sportiduino/sportiduino/img/BaseStationBatHolderFixed.jpg

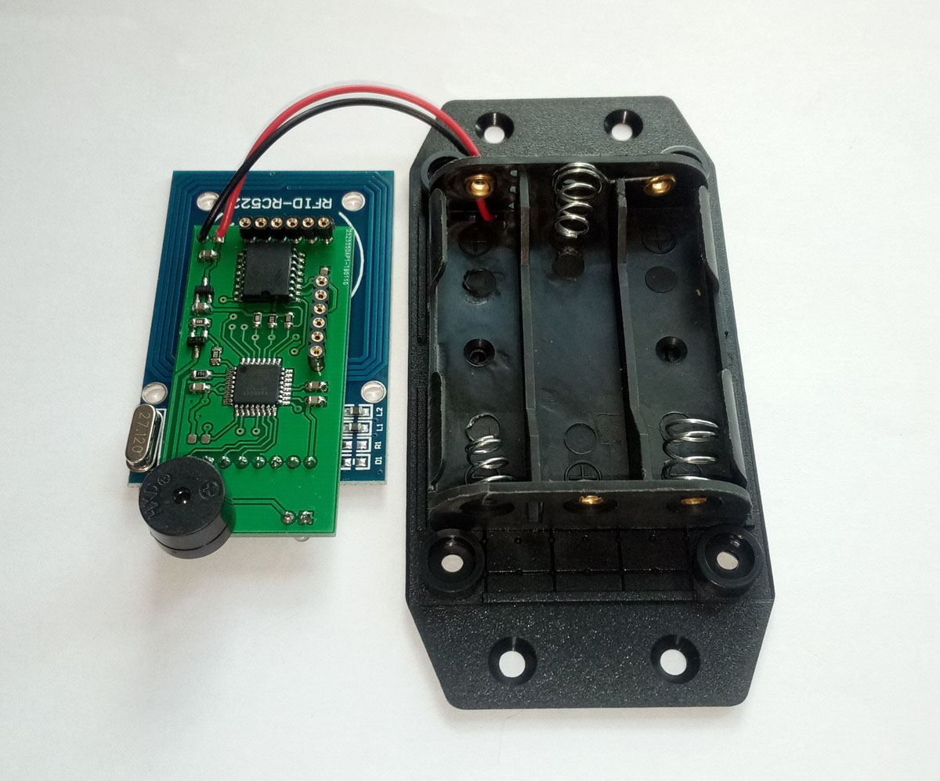
img/BaseStationBatHolderFixed.jpg
