sportiduino/sportiduino/img/BaseStationSerialConfConnect.jpg

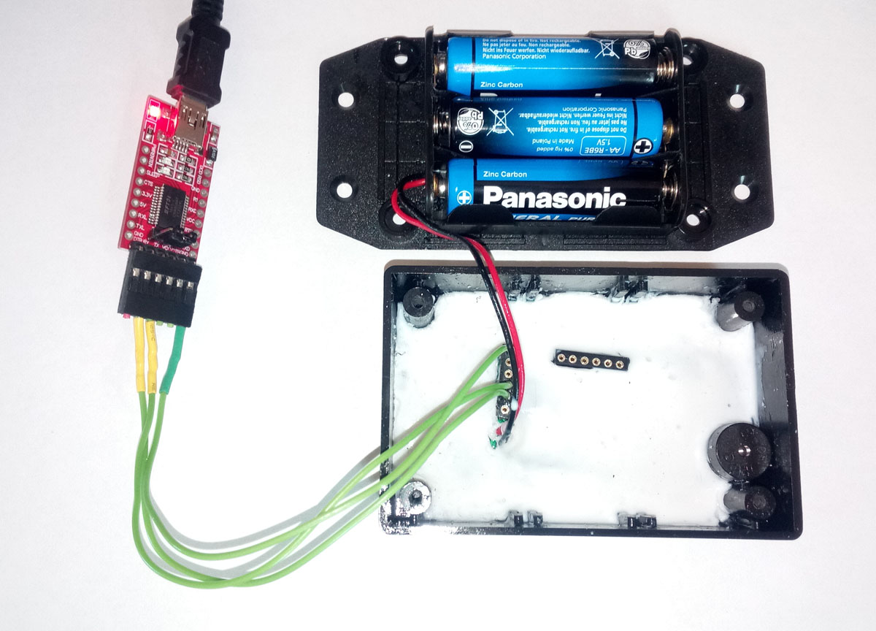
img/BaseStationSerialConfConnect.jpg
