sportiduino/sportiduino/img/BaseStationSoldedBottom.jpg

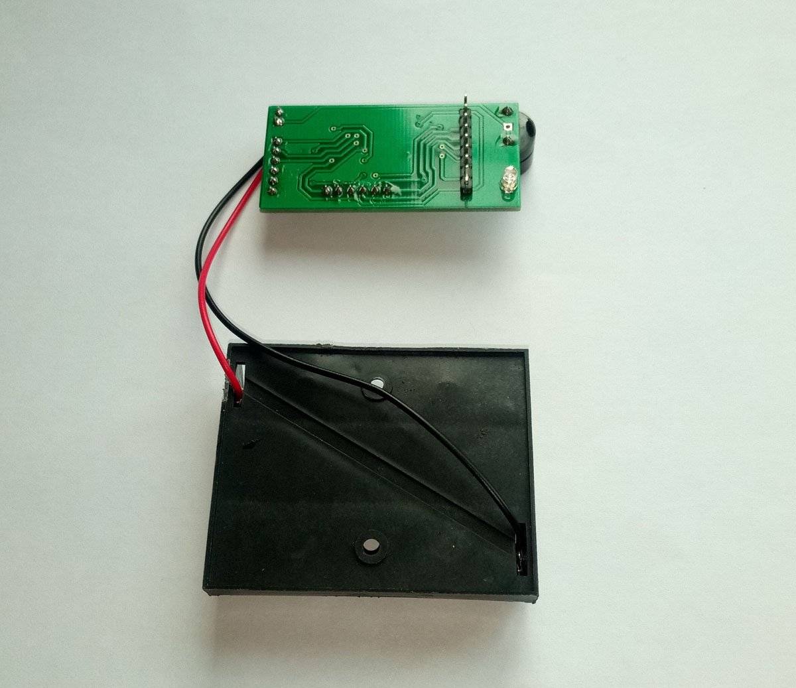
img/BaseStationSoldedBottom.jpg
