sportiduino/sportiduino/img/BaseStationSoldedTop.jpg

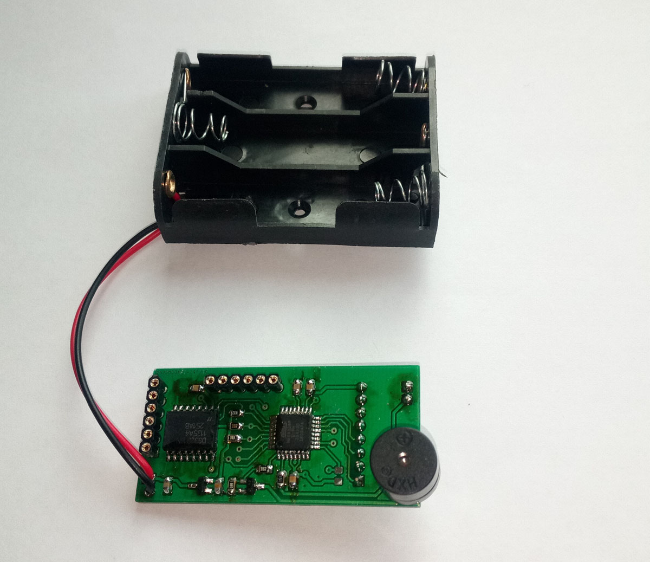
img/BaseStationSoldedTop.jpg
