sportiduino/sportiduino/img/Breadboard.JPG

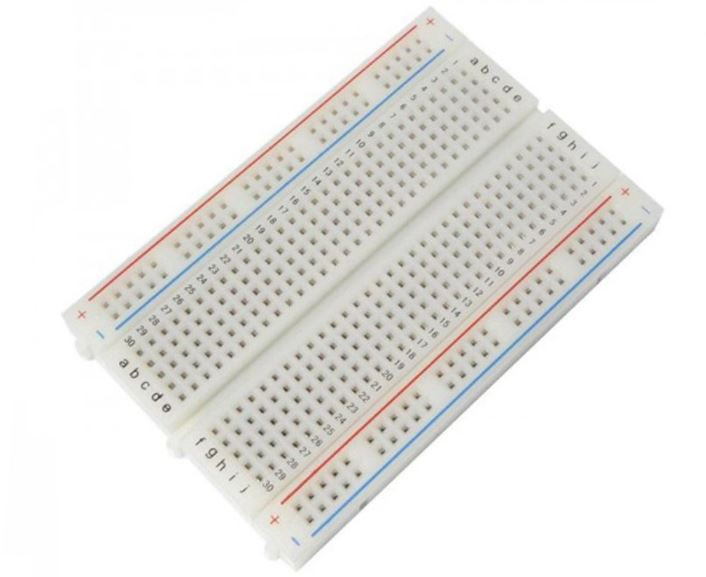
img/Breadboard.JPG
