sportiduino/sportiduino/img/ConfigWire.jpg

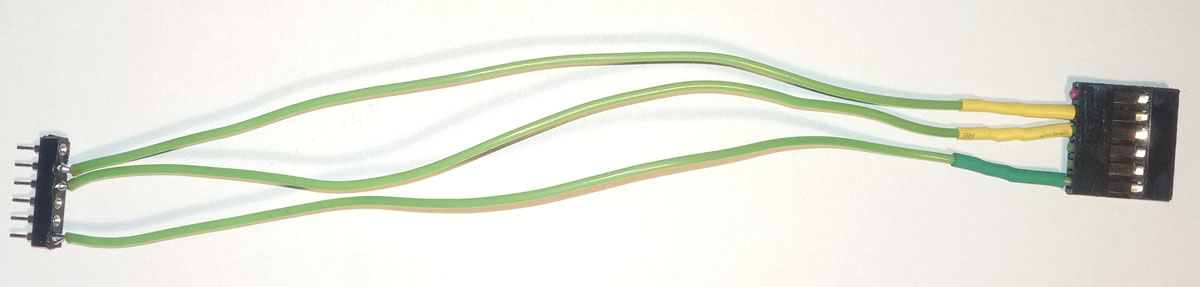
img/ConfigWire.jpg
