sportiduino/sportiduino/img/IntEEPROM.JPG

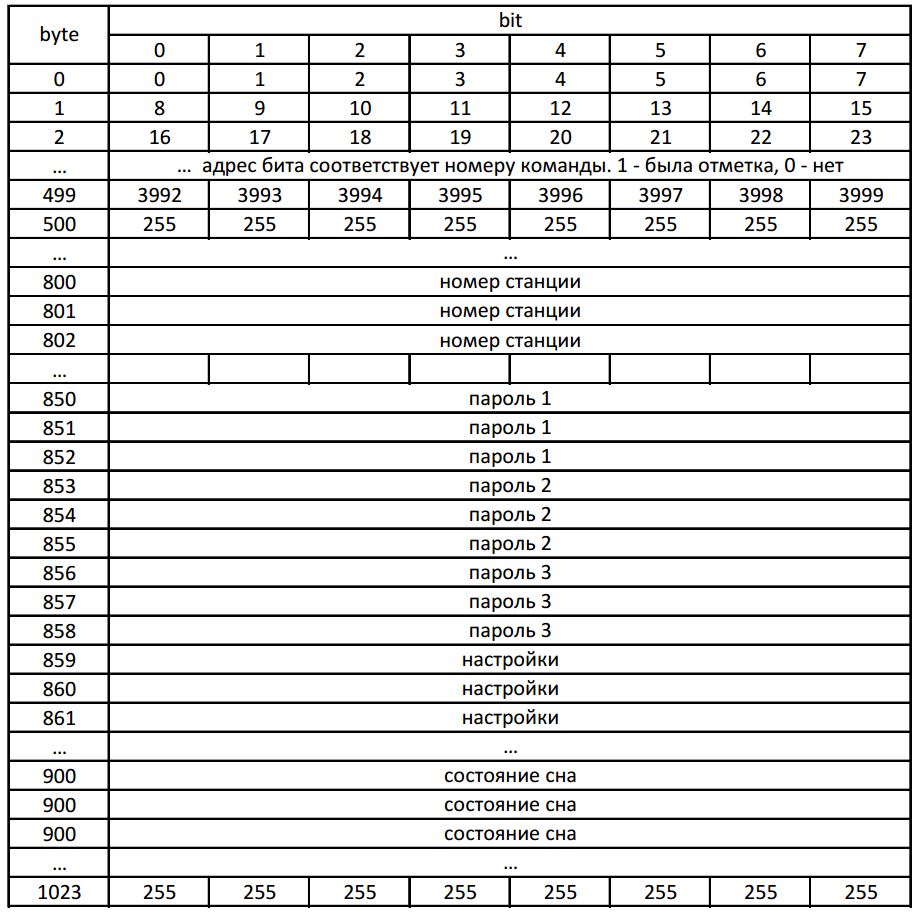
img/IntEEPROM.JPG
