sportiduino/sportiduino/img/ntag-dumpchip.jpg

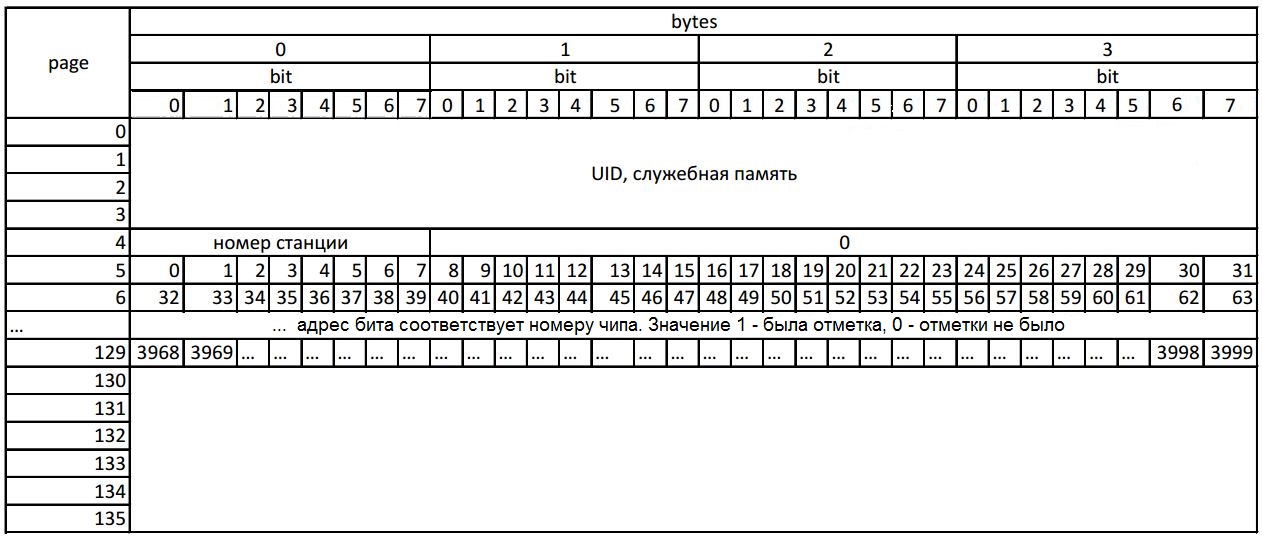
img/ntag-dumpchip.jpg
