sportiduino/sportiduino/img/pq_ru_master.png

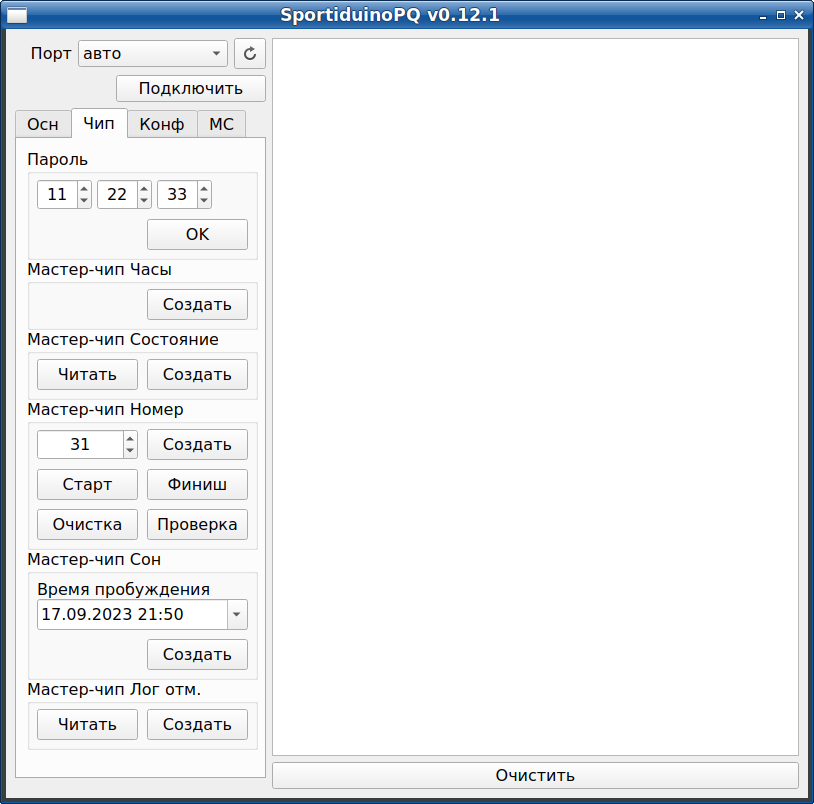
img/pq_ru_master.png
