sportiduino/sportiduino/img/s03.jpg

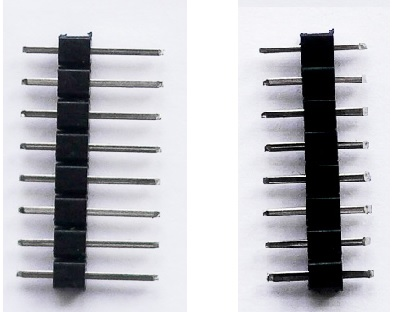
img/s03.jpg
