sportiduino/sportiduino/img/s04.jpg

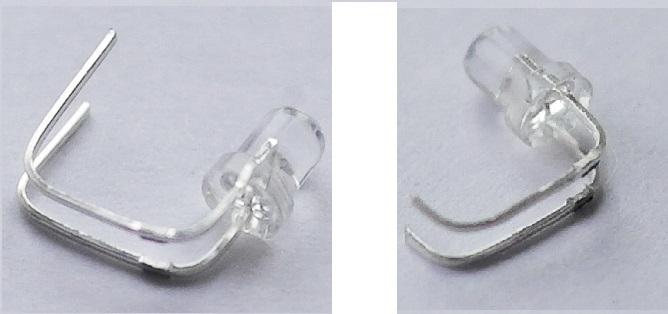
img/s04.jpg
