sportiduino/sportiduino/img/s05.jpg

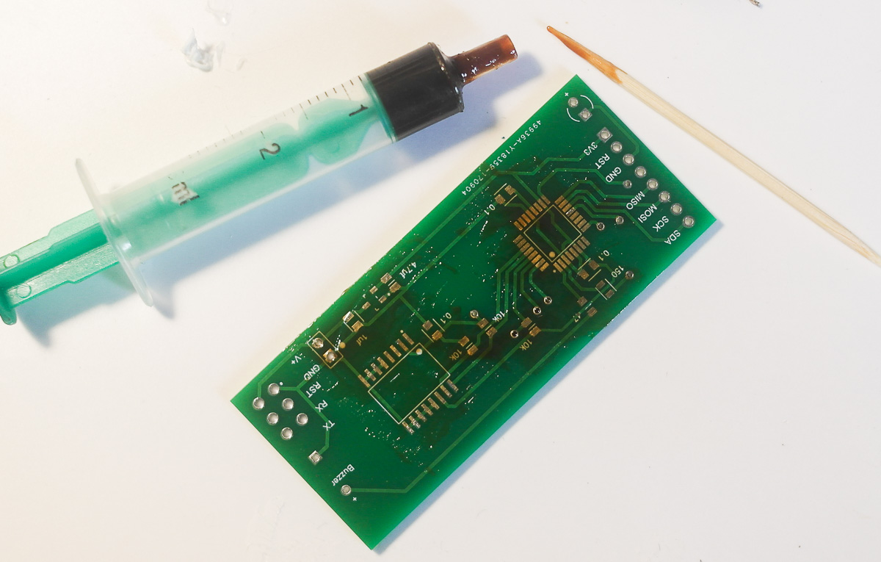
img/s05.jpg
