sportiduino/sportiduino/img/s06.jpg

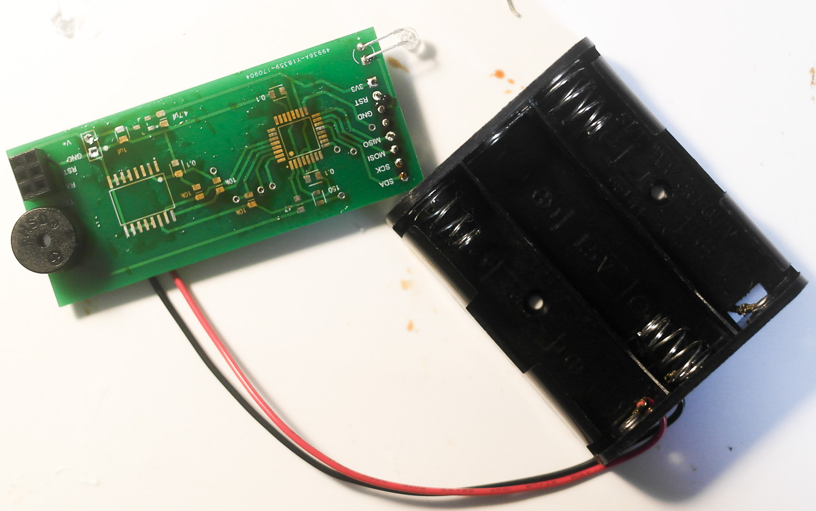
img/s06.jpg
