sportiduino/sportiduino/img/s07.jpg

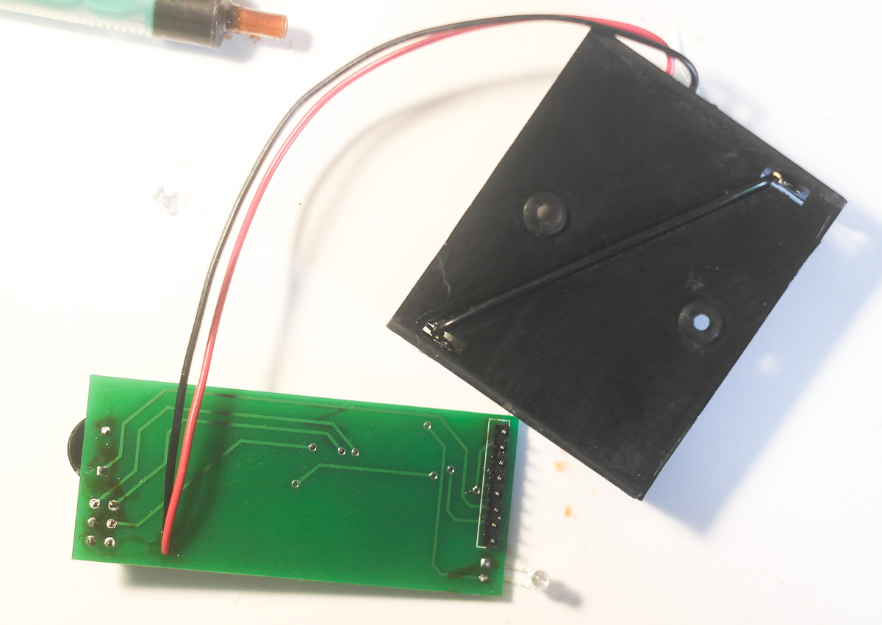
img/s07.jpg
