sportiduino/sportiduino/img/s09.jpg

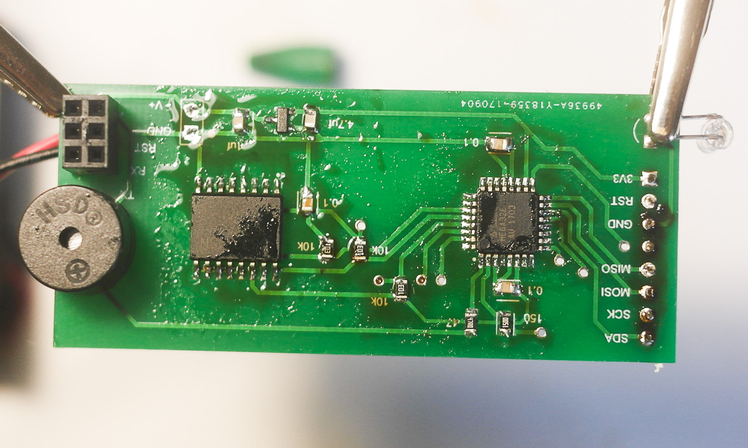
img/s09.jpg
