sportiduino/sportiduino/img/s10.jpg

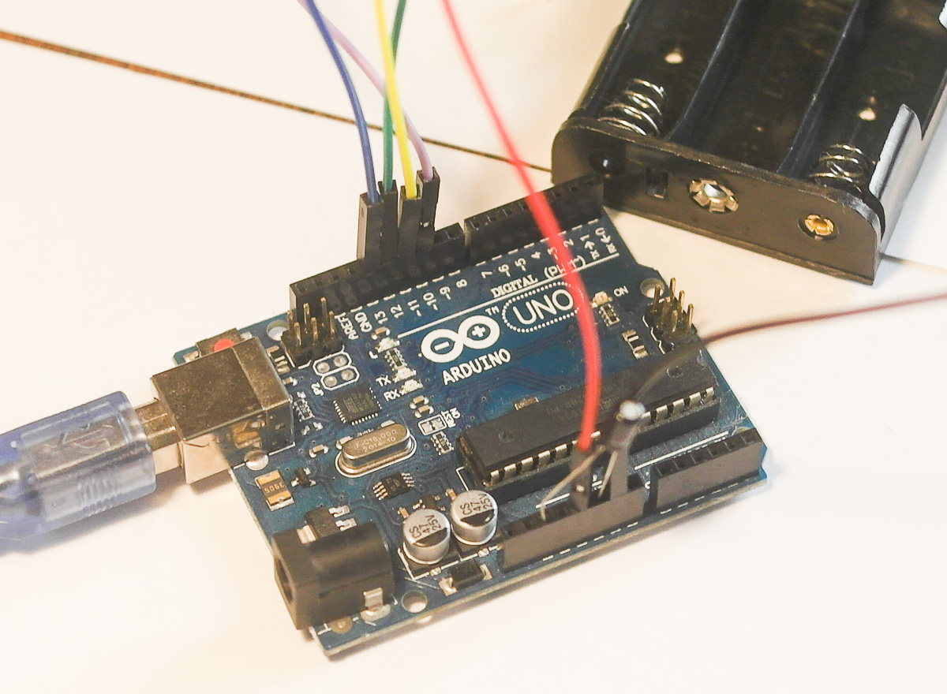
img/s10.jpg
