sportiduino/sportiduino/img/s11.jpg

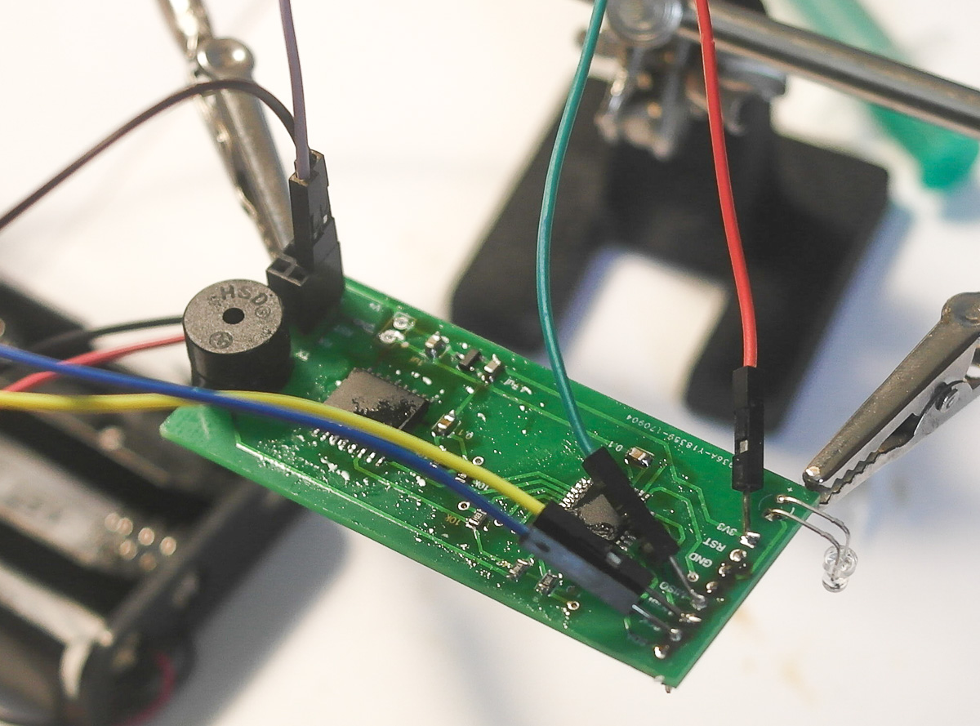
img/s11.jpg
