sportiduino/sportiduino/img/s12.jpg

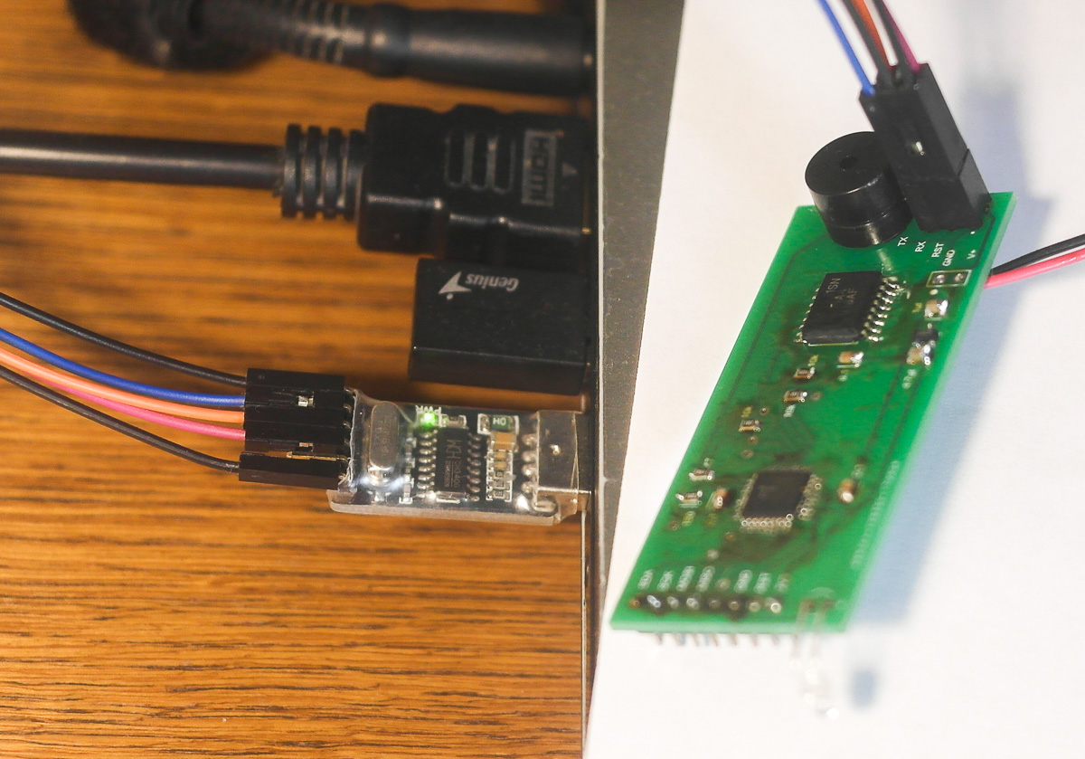
img/s12.jpg
