sportiduino/sportiduino/img/s13.jpg

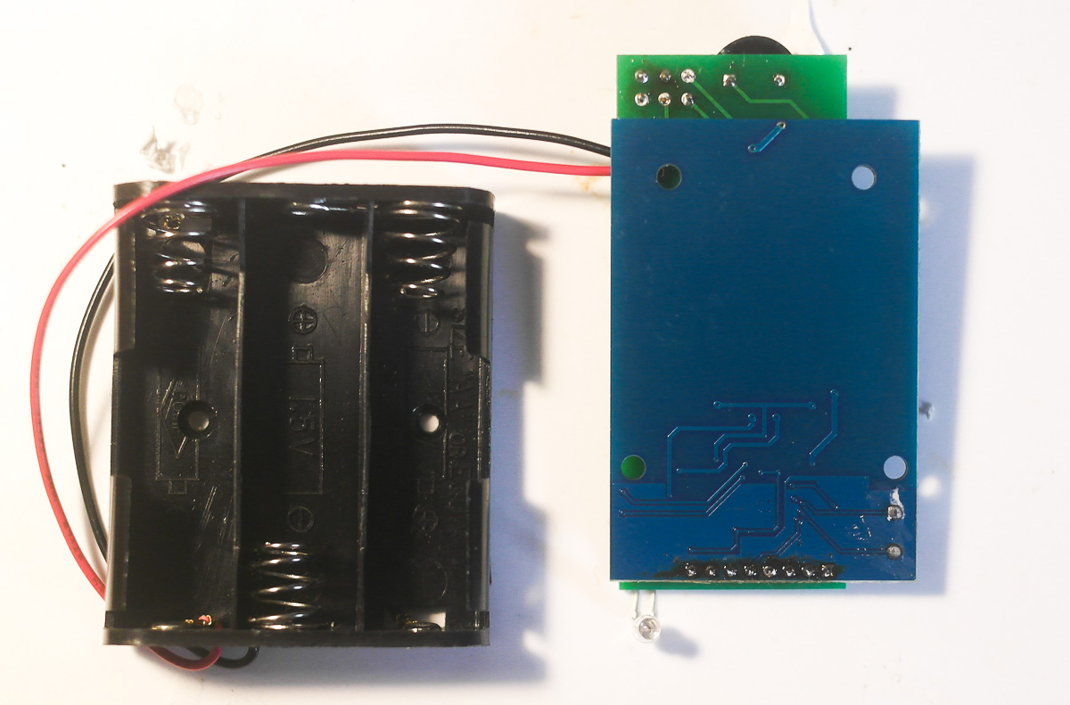
img/s13.jpg
