sportiduino/sportiduino/img/s14.jpg

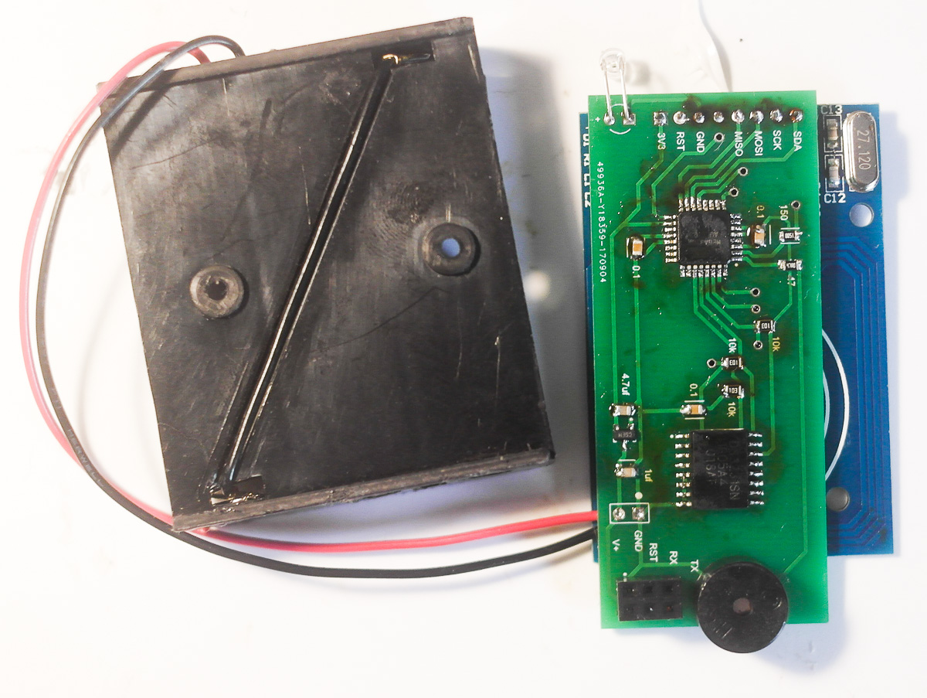
img/s14.jpg
