sportiduino/sportiduino/img/s15.jpg

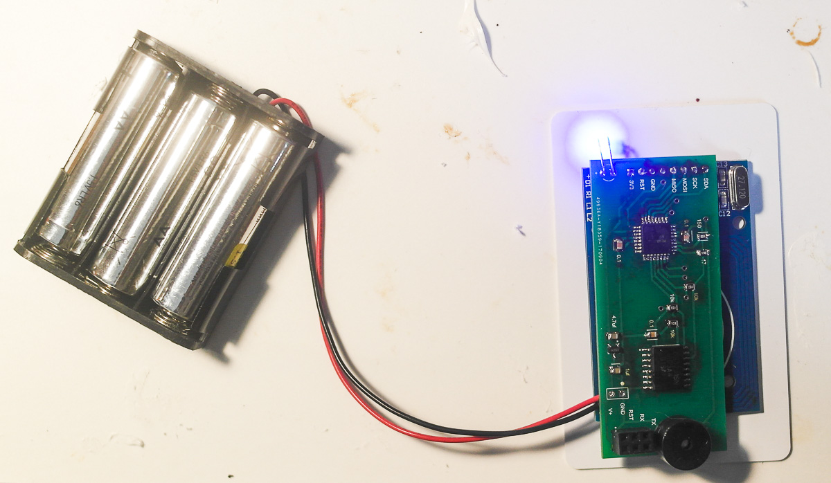
img/s15.jpg
