sportiduino/sportiduino/img/s16.jpg

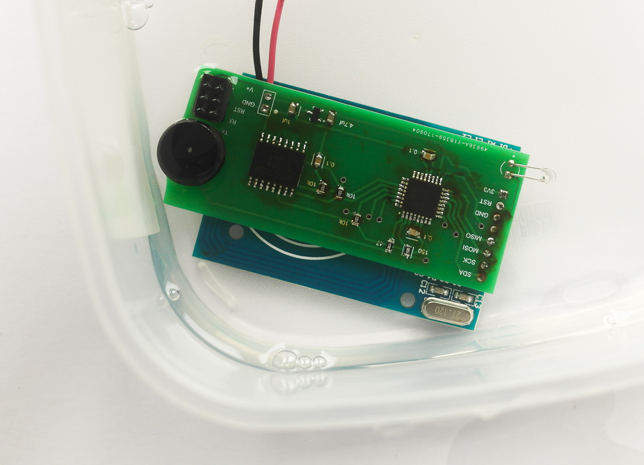
img/s16.jpg
