sportiduino/sportiduino/img/s17.jpg

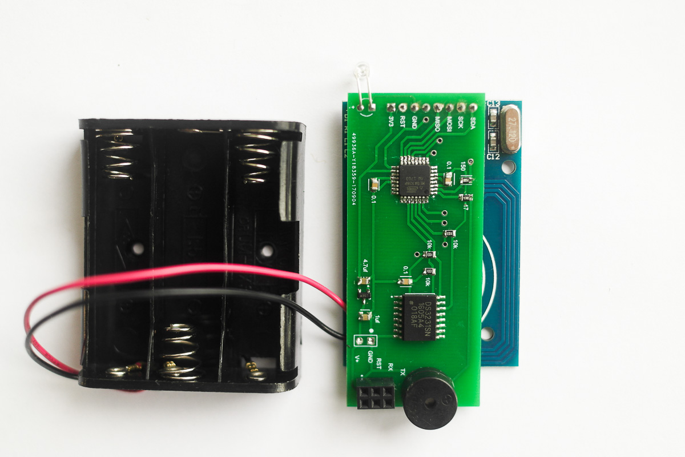
img/s17.jpg
