sportiduino/sportiduino/img/s18.jpg

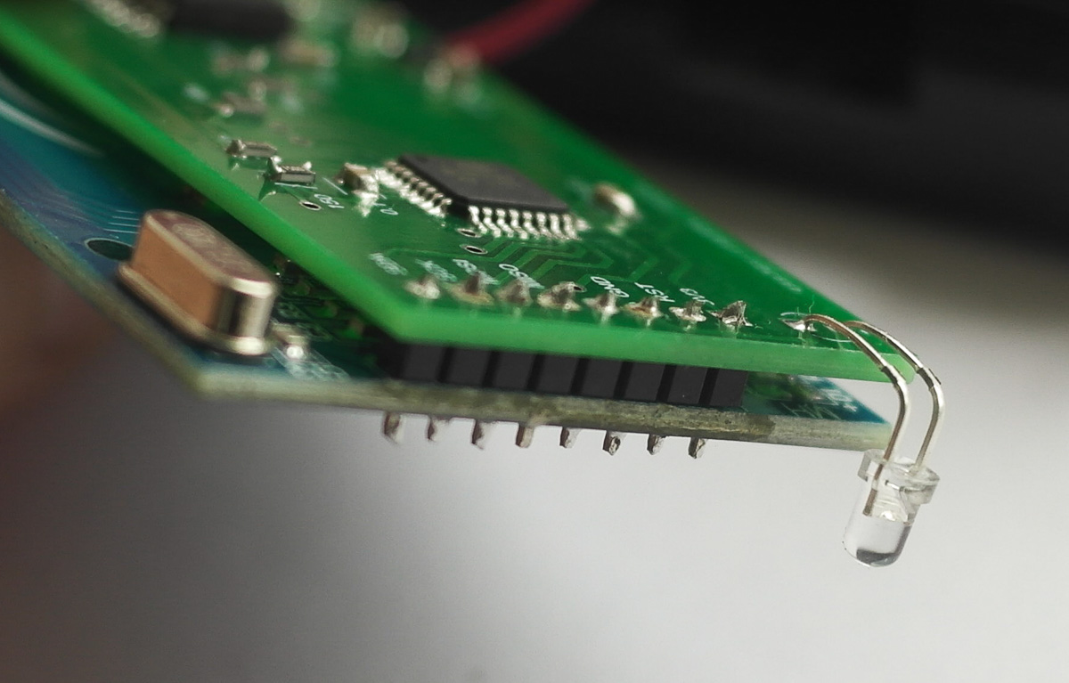
img/s18.jpg
