sportiduino/sportiduino/img/s19.jpg

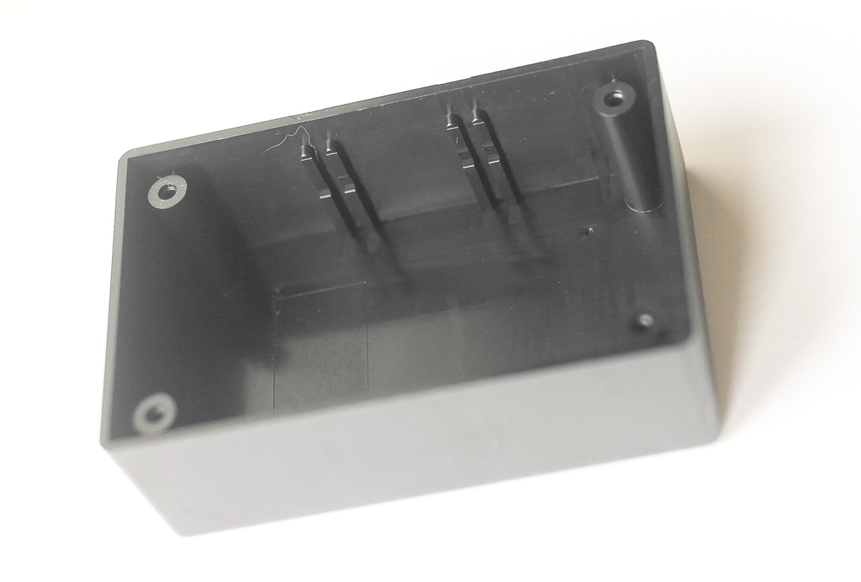
img/s19.jpg
