sportiduino/sportiduino/img/s20.jpg

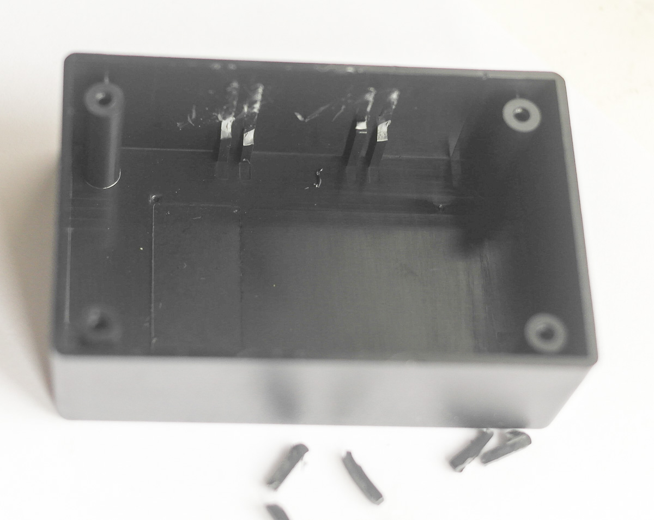
img/s20.jpg
