sportiduino/sportiduino/img/s21.jpg

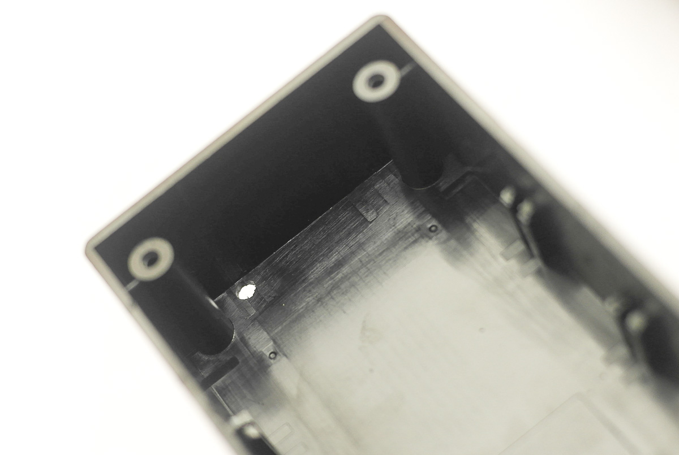
img/s21.jpg
