sportiduino/sportiduino/img/s22.jpg

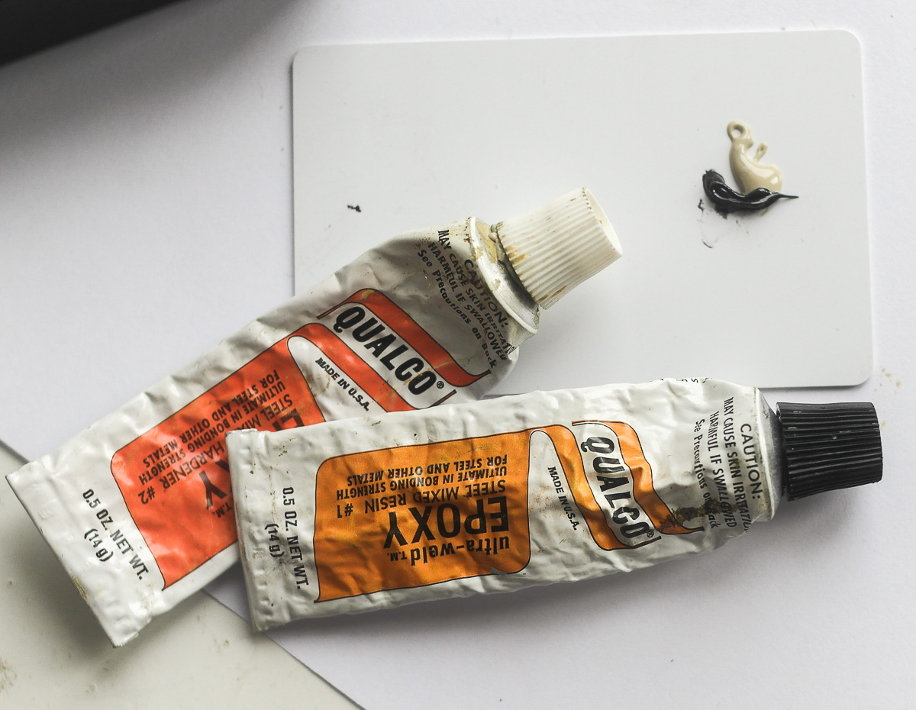
img/s22.jpg
