sportiduino/sportiduino/img/s23.jpg

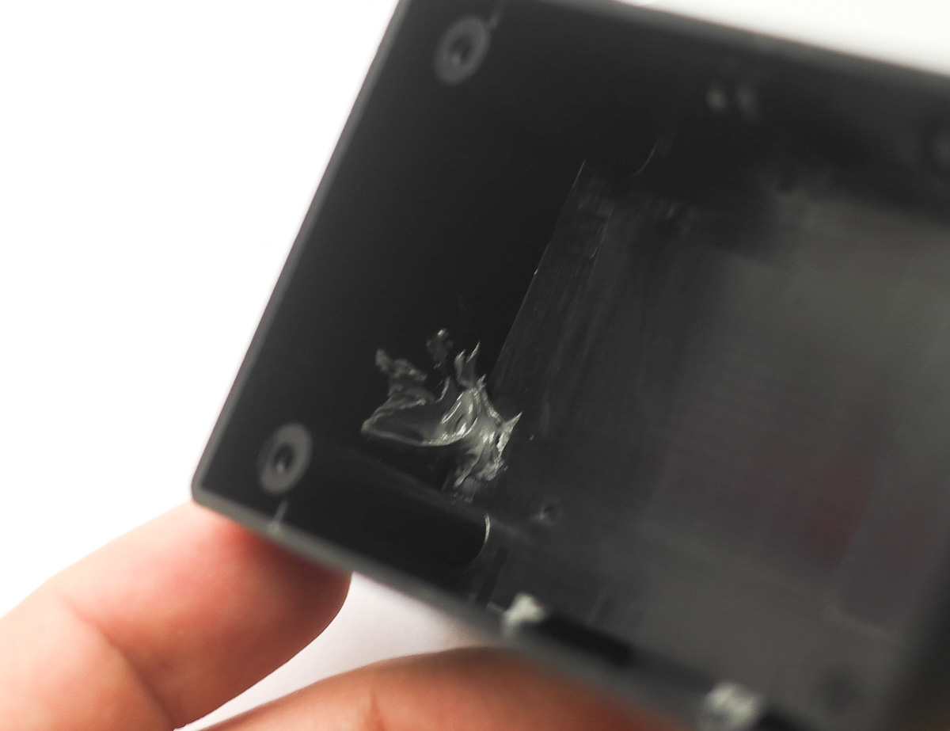
img/s23.jpg
