sportiduino/sportiduino/img/s24.jpg

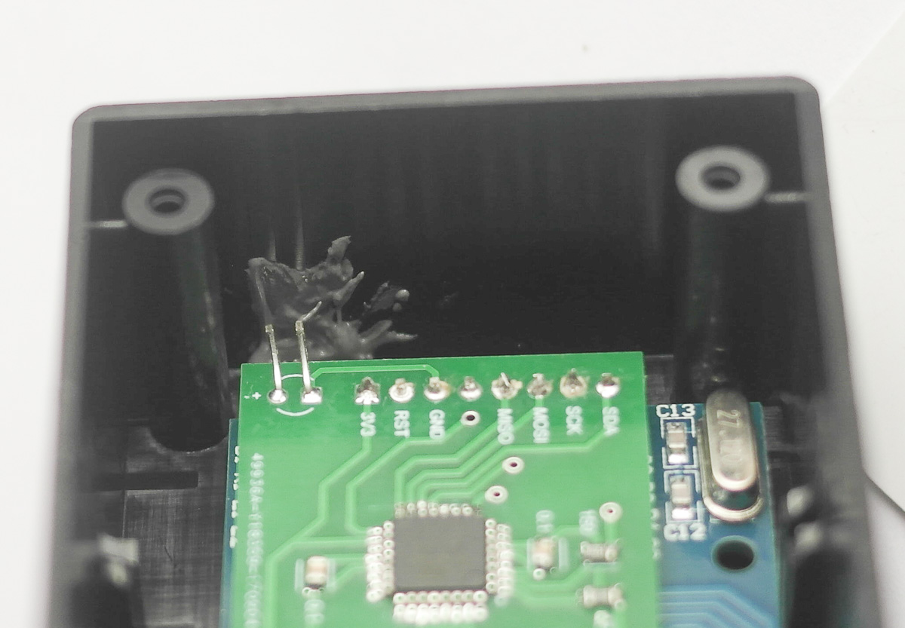
img/s24.jpg
