sportiduino/sportiduino/img/s25.jpg

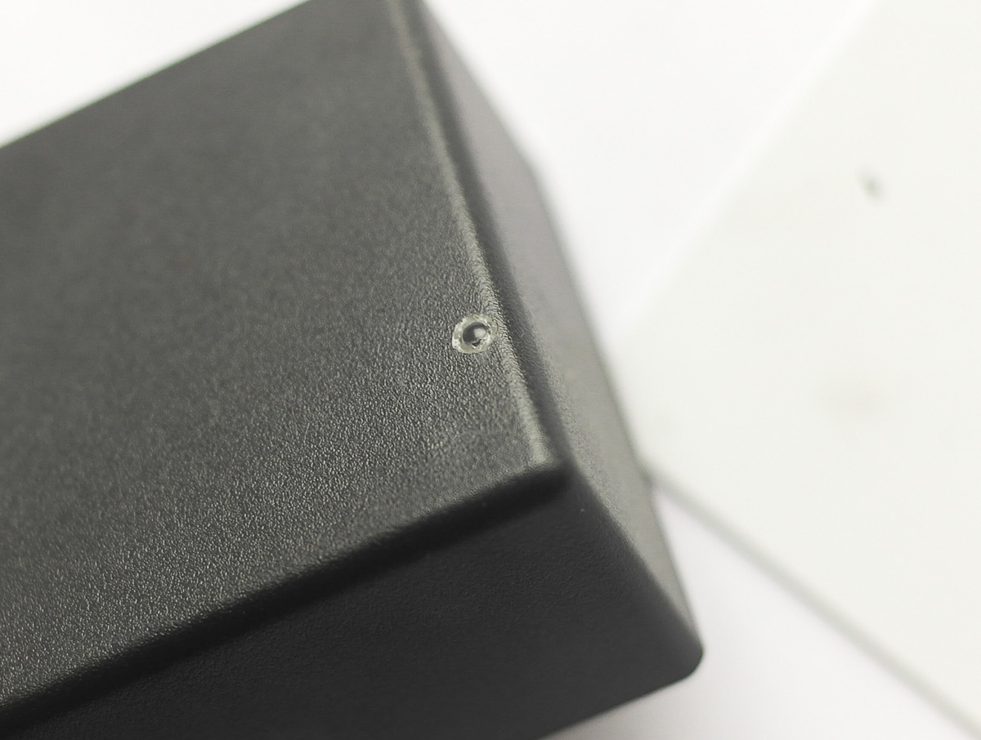
img/s25.jpg
