sportiduino/sportiduino/img/s33.jpg

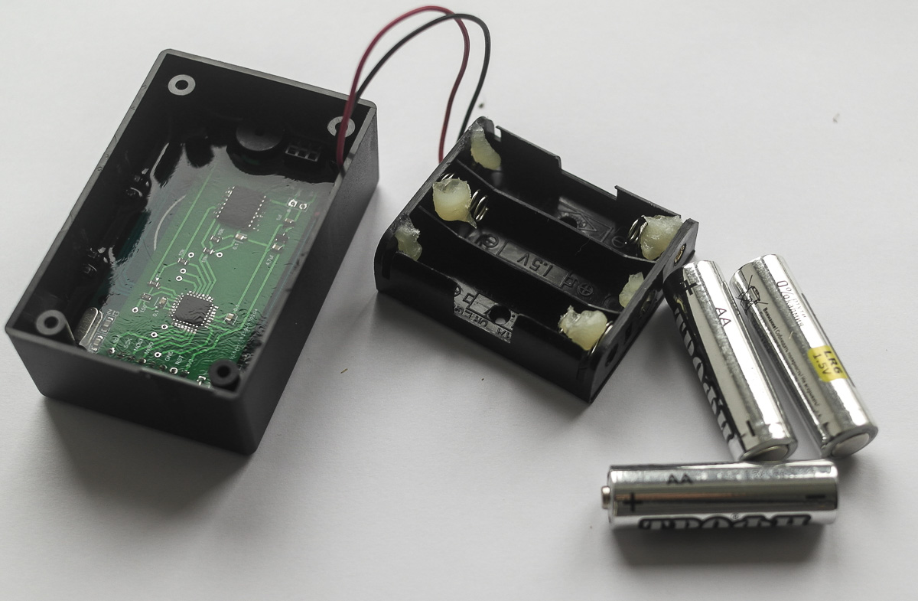
img/s33.jpg
