sportiduino/sportiduino/img/s37.jpg

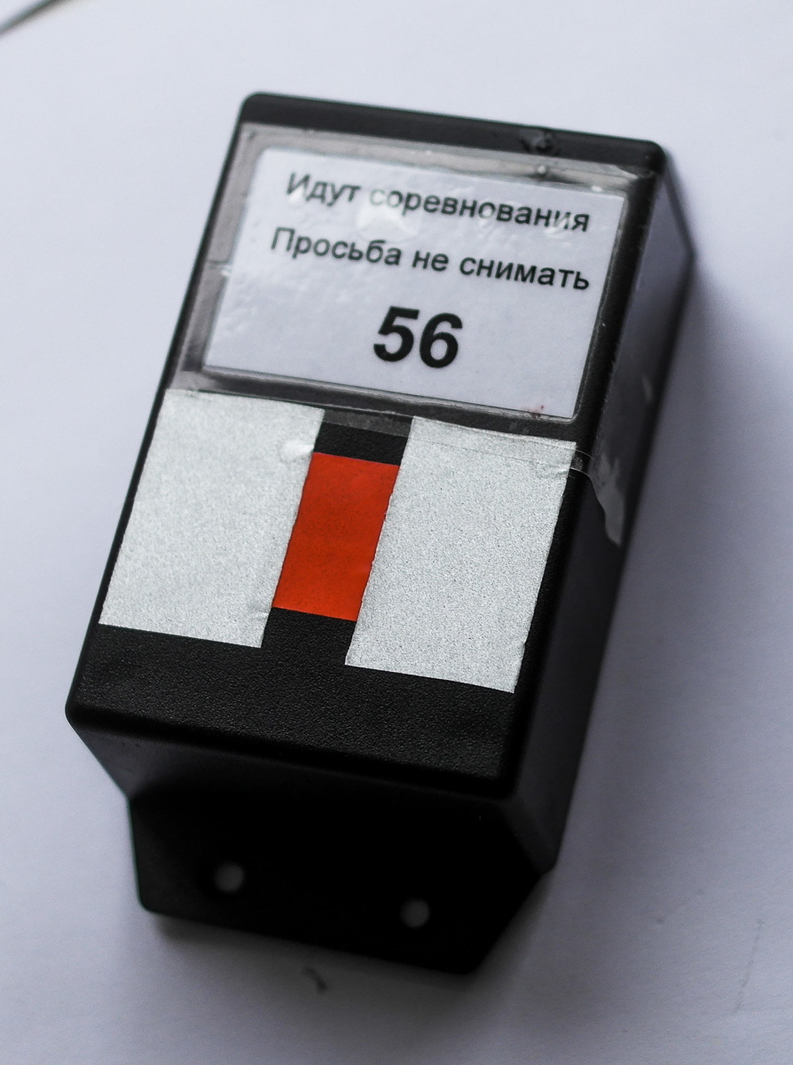
img/s37.jpg
