sportiduino/sportiduino/img/Setting-byte2.PNG

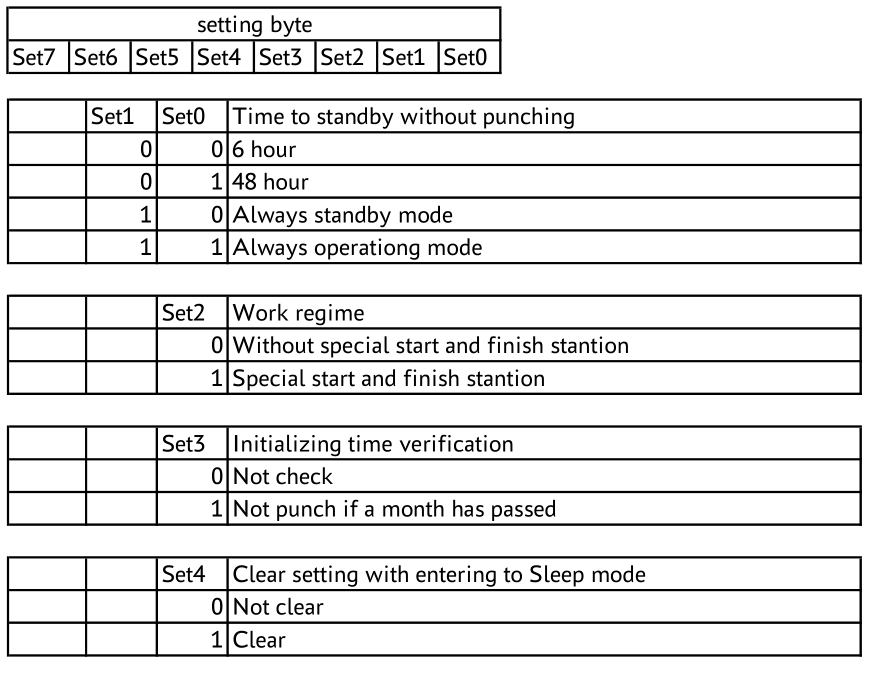
img/Setting-byte2.PNG
