sportiduino/sportiduino/img/UNO.JPG

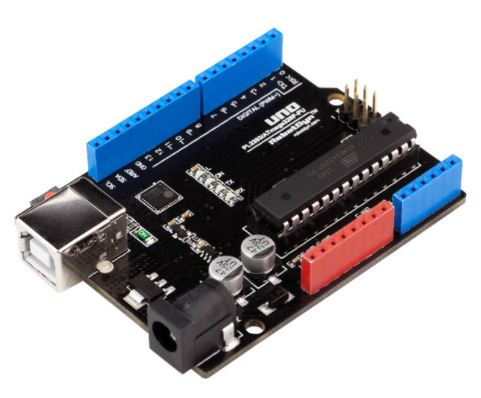
img/UNO.JPG
