sportiduino/sportiduino/img/Wire.JPG

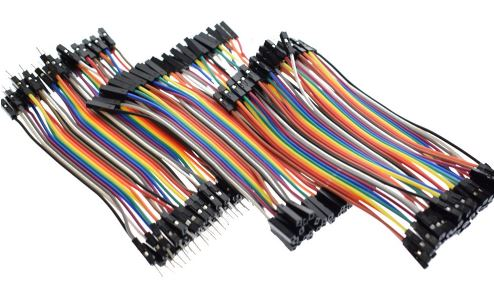
img/Wire.JPG
